ese-519/Content-Reactive-Humanoid-Toy-Figures/Devpost/IMG_4884.JPG

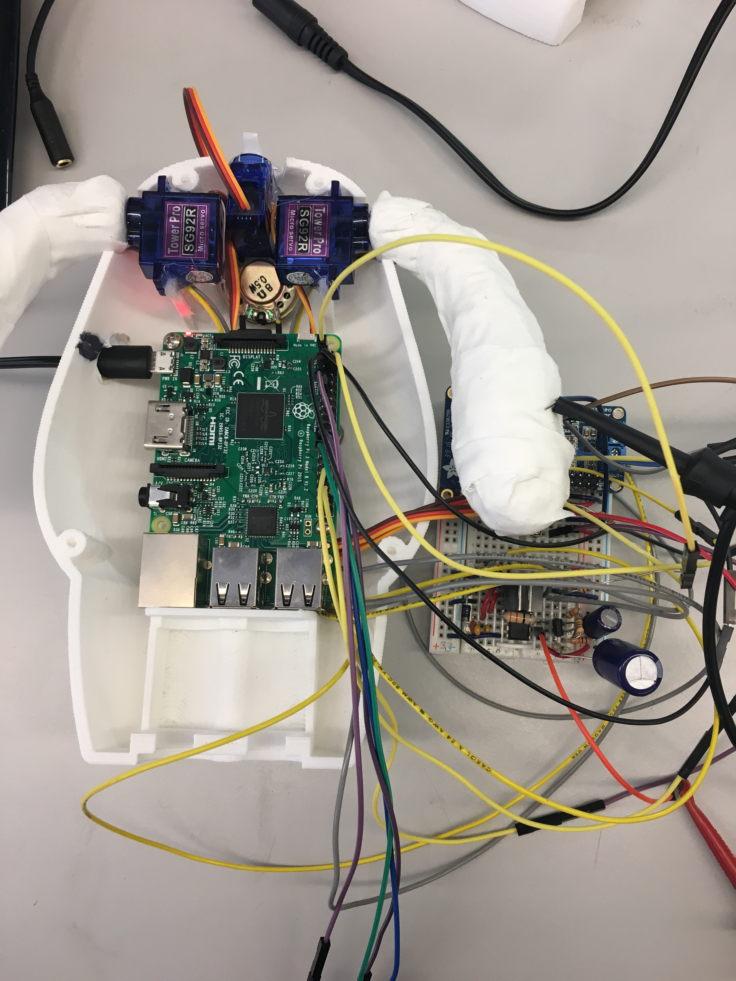
Devpost/IMG_4884.JPG
