ese-519/Content-Reactive-Humanoid-Toy-Figures/Images/IMG_5679.JPG

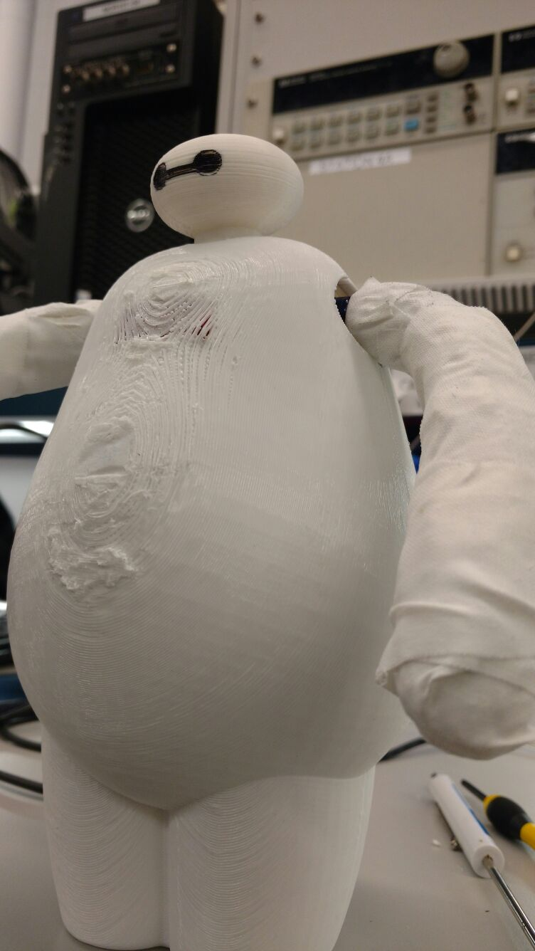
Images/IMG_5679.JPG
