ese-519/Content-Reactive-Humanoid-Toy-Figures/Images/IMG_20161202_160459102.jpg

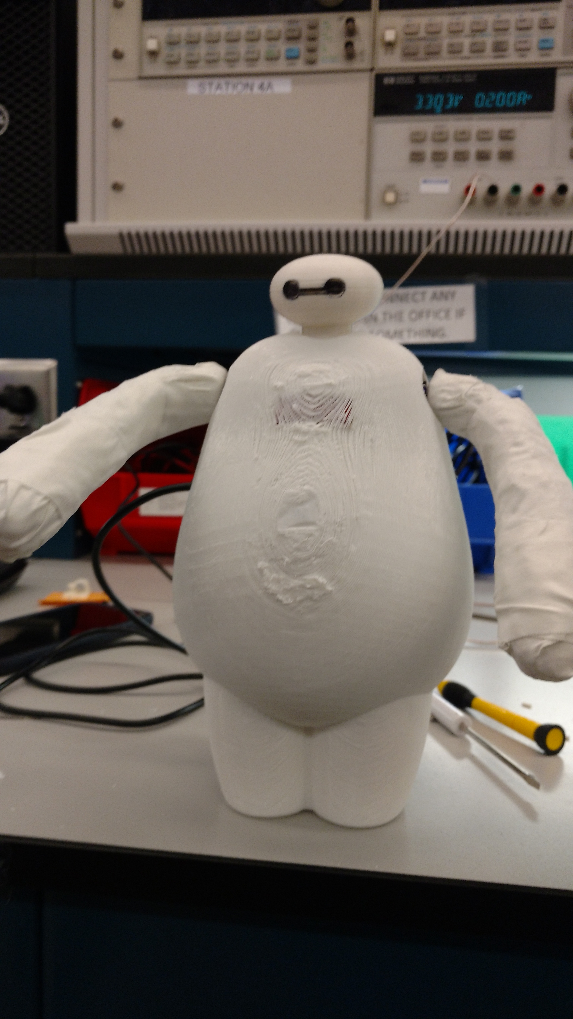
Images/IMG_20161202_160459102.jpg
