ese-519/Content-Reactive-Humanoid-Toy-Figures/ReachGoalDemo/CADFiles/sideView_baymax.jpg

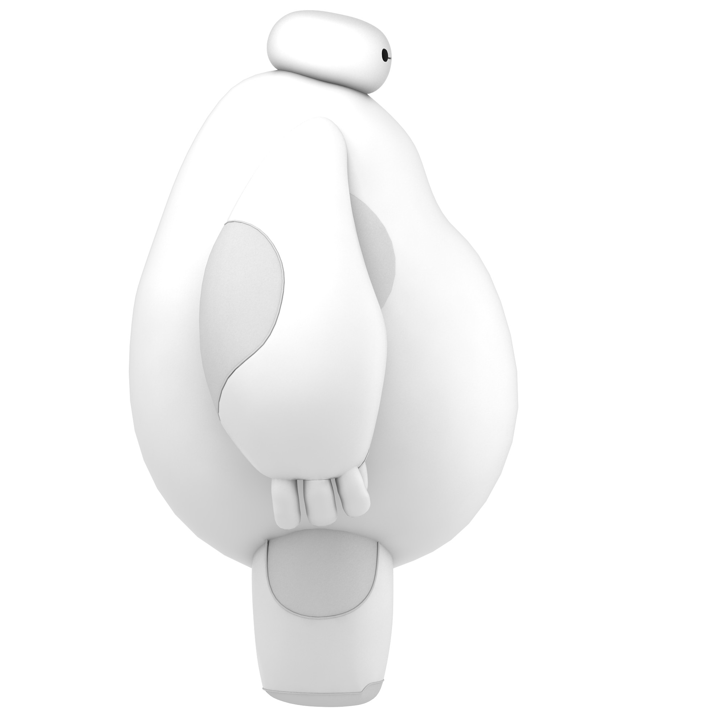
ReachGoalDemo/CADFiles/sideView_baymax.jpg
