ese-519/Content-Reactive-Humanoid-Toy-Figures/BaselineDemo/CADFiles/headFront.SLDPRT

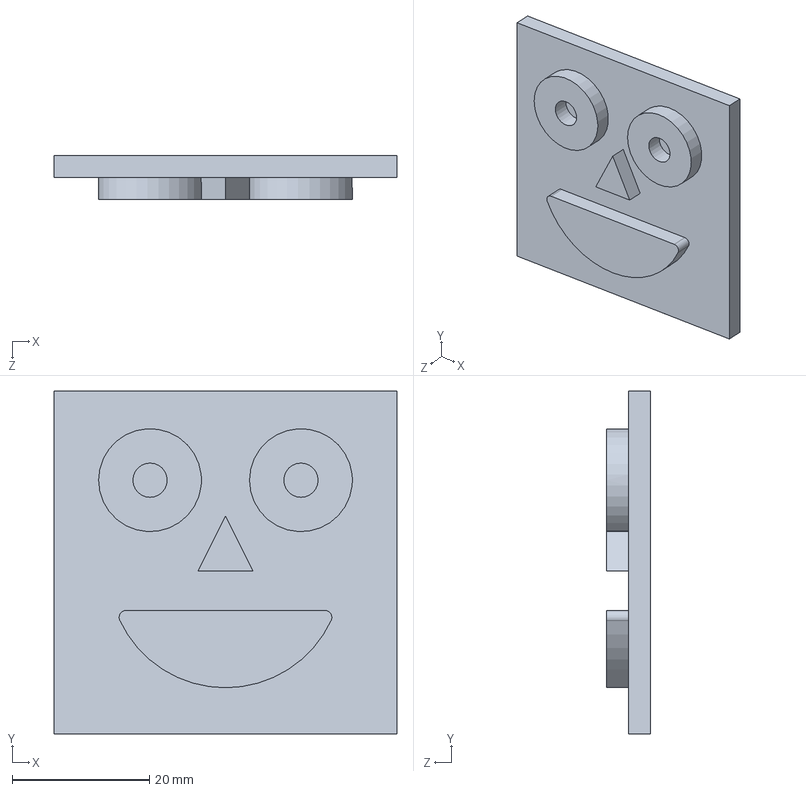
[picture p33: CAD file, 2016-12-07]
BaselineDemo/CADFiles/headFront.SLDPRT
50.0 x 50.0 x 6.35 mm
