ese-519/Content-Reactive-Humanoid-Toy-Figures/ReachGoalDemo/CADFiles/rightArmBack.sldprt

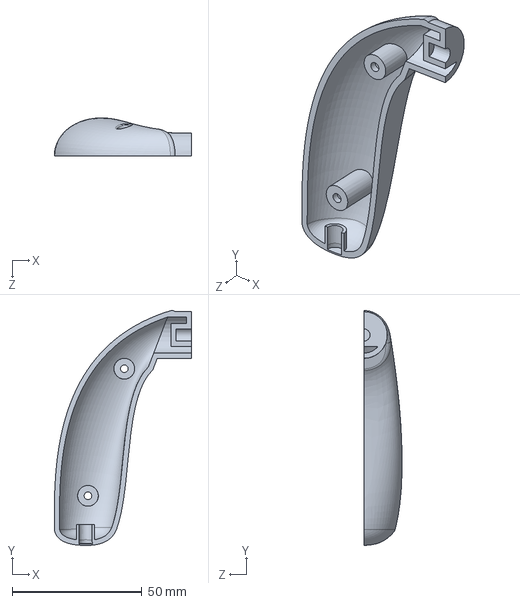
[picture p34: CAD file, 2016-12-07]
ReachGoalDemo/CADFiles/rightArmBack.sldprt
53.0 x 90.6 x 14.7 mm
