ese-519/Content-Reactive-Humanoid-Toy-Figures/BaselineDemo/CADFiles/headTop.SLDPRT

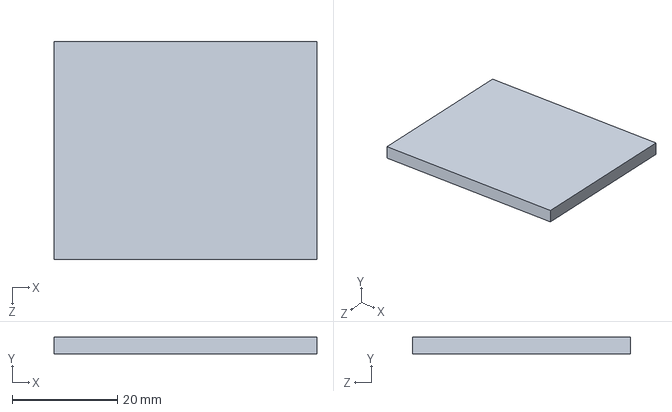
[picture p35: CAD file, 2016-12-07]
BaselineDemo/CADFiles/headTop.SLDPRT
50.0 x 3.17 x 41.3 mm
