ese-519/Content-Reactive-Humanoid-Toy-Figures/BaselineDemo/CADFiles/pcbBracket.SLDPRT

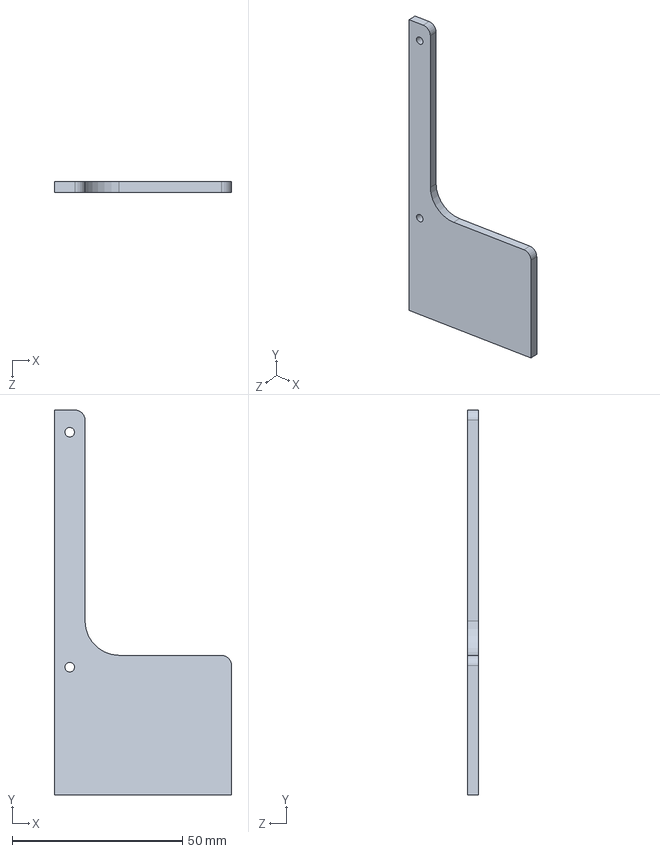
[picture p36: CAD file, 2016-12-07]
BaselineDemo/CADFiles/pcbBracket.SLDPRT
52.0 x 113.0 x 3.17 mm
