ese-519/Content-Reactive-Humanoid-Toy-Figures/ReachGoalDemo/CADFiles/arm.SLDPRT

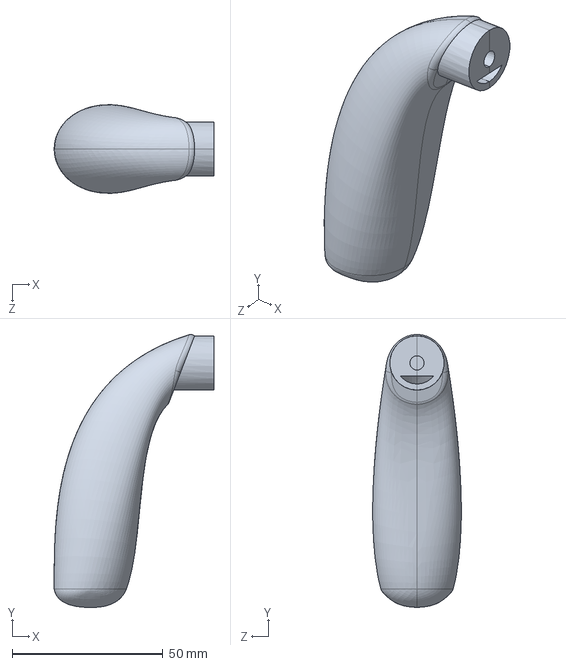
[picture p37: CAD file, 2016-12-07]
ReachGoalDemo/CADFiles/arm.SLDPRT
53.0 x 90.6 x 29.4 mm
