ese-519/Content-Reactive-Humanoid-Toy-Figures/BaselineDemo/CADFiles/motorTop.SLDPRT

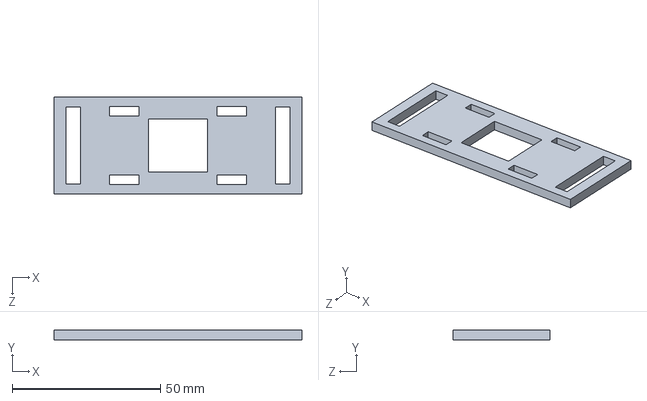
[picture p38: CAD file, 2016-12-07]
BaselineDemo/CADFiles/motorTop.SLDPRT
83.7 x 3.25 x 32.7 mm
