ese-519/Content-Reactive-Humanoid-Toy-Figures/BaselineDemo/CADFiles/top_bottom.SLDPRT

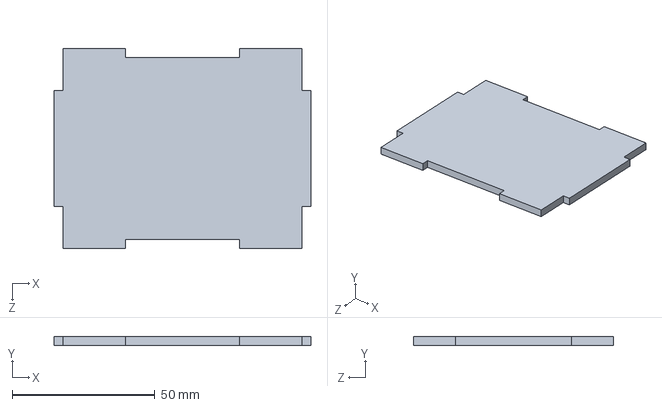
[picture p39: CAD file, 2016-12-07]
BaselineDemo/CADFiles/top_bottom.SLDPRT
90.0 x 3.17 x 70.0 mm
