ese-519/Content-Reactive-Humanoid-Toy-Figures/ReachGoalDemo/CADFiles/body_front.sldprt

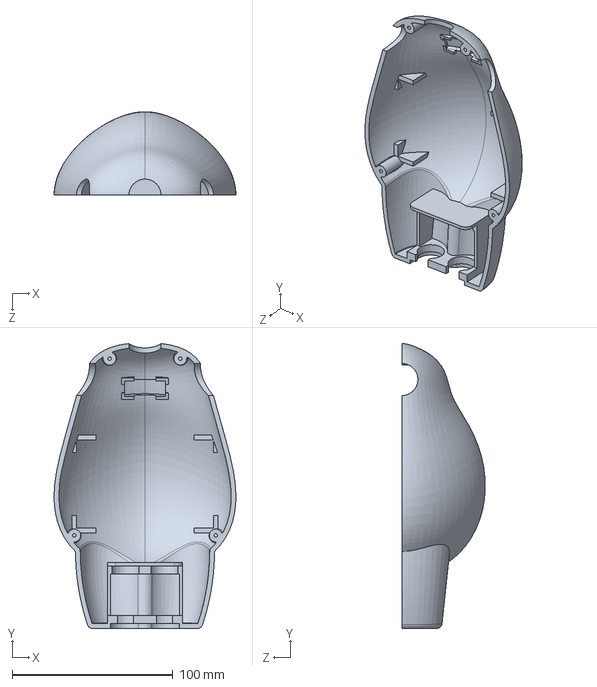
[picture p40: CAD file, 2016-12-07]
ReachGoalDemo/CADFiles/body_front.sldprt
113.1 x 177.3 x 51.9 mm
