ese-519/Content-Reactive-Humanoid-Toy-Figures/BaselineDemo/CADFiles/batteryTop.SLDPRT

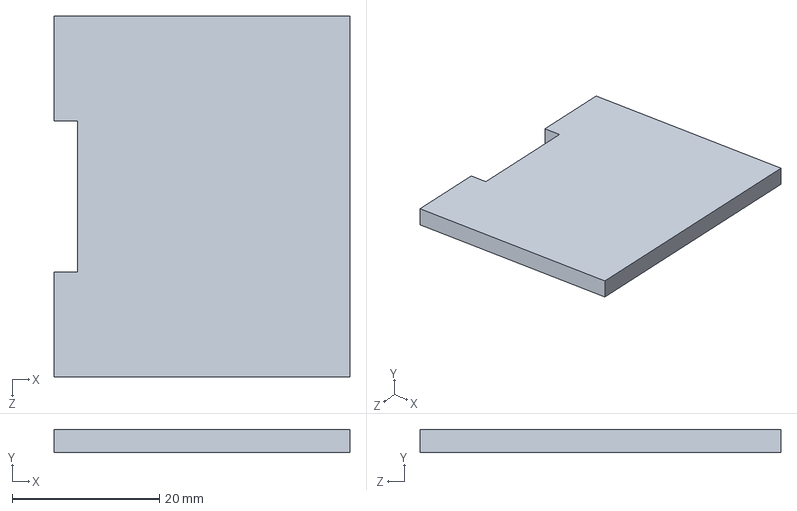
[picture p41: CAD file, 2016-12-07]
BaselineDemo/CADFiles/batteryTop.SLDPRT
40.2 x 3.17 x 49.0 mm
