ese-519/Content-Reactive-Humanoid-Toy-Figures/BaselineDemo/CADFiles/front.SLDPRT

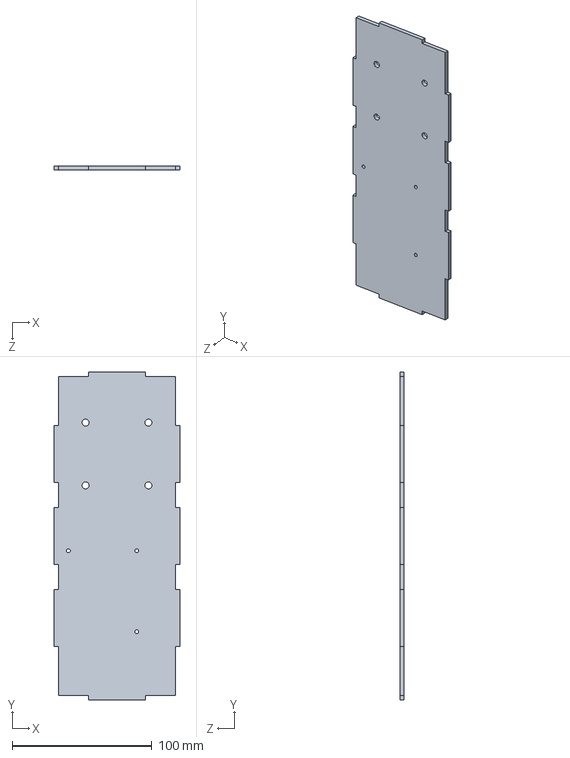
[picture p42: CAD file, 2016-12-07]
BaselineDemo/CADFiles/front.SLDPRT
90.0 x 235.0 x 3.17 mm
