ese-519/Content-Reactive-Humanoid-Toy-Figures/BaselineDemo/Codes/playvideo.py

import numpy as np
import cv2

cap = cv2.VideoCapture('/home/sarath/Desktop/ESE519/video1.mp4')
print "hey"
while(cap.isOpened()):
	
	ret, frame = cap.read()
	gray = cv2.cvtColor(frame, cv2.COLOR_BGR2GRAY)
	cv2.imshow('frame',gray)
	if cv2.waitKey(30) & 0xFF == ord('q'):
		break

cap.release()
cv2.destroyAllWindows()
